opiopan/elflet/firmware/main/JsonTags.cpp

#include "Config.h"

const char JSON_CONFIGVERSION[] = "ConfigVersion";
const char JSON_FUNCTIONMODE[] = "FunctionMode";
const char JSON_BOARDTYPE[] = "BoardType";
const char JSON_BOARDVERSION[] = "BoardVersion";
const char JSON_FWVERSION[] = "FirmwareVersion";
const char JSON_FWVERSION_MAJOR[] = "major";
const char JSON_FWVERSION_MINOR[] = "minor";
const char JSON_FWVERSION_BUILD[] = "build";
const char JSON_FWURI[] = "FirmwareUri";

const char JSON_NODENAME[] = "NodeName";
const char JSON_APSSID[] = "AP_SSID";
const char JSON_ADMINPASSWORD[] = "AdminPassword";
const char JSON_SSID[] = "SSID";
const char JSON_WIFIPASSWORD[] = "WiFiPassword";
const char JSON_COMMIT[] = "commit";
const char JSON_NTPSERVER[] = "NTPServer";
const char JSON_TIMEZONE[] = "Timezone";

const char JSON_PUBSUB[] = "PubSub";
const char JSON_SENSORFREQUENCY[] = "SensorFrequency";
const char JSON_PUBSUBSERVERADDR[] = "PubSubServerAddr";
const char JSON_PUBSUBSESSIONTYPE[] = "PubSubSessionType";
const char JSON_PUBSUBSERVERCERT[] = "PubSubServerCert";
const char JSON_PUBSUBUSER[] = "PubSubUser";
const char JSON_PUBSUBPASSWORD[] = "PubSubPassword";
const char JSON_SENSORTOPIC[] = "SensorTopic";
const char JSON_IRRCRECEIVETOPIC[] = "IrrcReceiveTopic";
const char JSON_IRRCRECEIVEDDATATOPIC[] = "IrrcReceivedDataTopic";
const char JSON_IRRCSENDTOPIC[] = "IrrcSendTopic";
const char JSON_DOWNLOADFIRMWARETOPIC[] = "DownloadFirmwareTopic";
const char JSON_SHADOWTOPIC[] = "ShadowTopic";

const char JSON_IRRCRECEIVERMODE[] = "IrrcReceiverMode";
const char JSON_WIFI[] = "EnableWiFi";
const char JSON_BLEHID[] = "EnableBLEHID";

const char JSON_BUTTON_MODE[] = "ButtonMode";
const char JSON_BUTTON_BLEHIDCODE[] = "ButtonBleHidCode";

const char JSON_DATE[] = "date";
const char JSON_TEMP_UNIT[] = "temperatureUnit";
const char JSON_HUM_UNIT[] = "humidityUnit";
const char JSON_PRESS_UNIT[] = "pressureUnit";
const char JSON_LUMINO_UNIT[] = "luminosityeUnit";
const char JSON_TEMP[] = "temperature";
const char JSON_HUM[] = "humidity";
const char JSON_PRESS[] = "pressure";
const char JSON_LUMINO[] = "luminositye";

const char JSON_FORMATED[] = "FormatedIRStream";
const char JSON_PROTOCOL[] = "Protocol";
const char JSON_BITCOUNT[] = "BitCount";
const char JSON_DATA[] = "Data";
const char JSON_RAW[] = "RawIRStream";
const char JSON_LEVEL[] = "Level";
const char JSON_DURATION[] = "Duration";
