opiopan/elflet/firmware/main/foundations/htdigestfs.h

#pragma once

#include <stdint.h>
#include <stdio.h>

#define HTDIGESTLENGTH 16

#ifdef __cplusplus
extern "C" {
#endif
    
void htdigestfs_init(const char* mp);
void htdigestfs_register(const char* user, const char* domain,
                         const char* pass);
FILE* htdigestfs_fp();

#ifdef __cplusplus
}
#endif
